akkoyun/WeatherStat_Industrial_Design/P101DA-Rain/M401AA/Readme.md

# H701AA Kepçe Pimi ve Sekmanı  &nbsp; &nbsp; 
| Parça Kodu | Parça Açıklaması | Parça Boyutları | Parça Malzemesi  | Kullanım Adedi |
|---|---|---|---|---|
| H701AA | Kepçe Pimi | ? | Paslanmaz  ? | 1 |
| H602AA | Kepçe Pimi Sekmanı | DIN 6799 Ay Segman 4 mm| Paslanmaz | 2 |

## Açıklama
[Kepçe](../C123AA/Readme.md) , [Alt Gövde](../C122AA/Readme.md)'ye bu Kepçe pimi ile bağlanır.</br>
Pim uçları 4mm DIN 6799 Ay Segman ile sonlandırılır. </br>
# __
### Kepçe Pimi
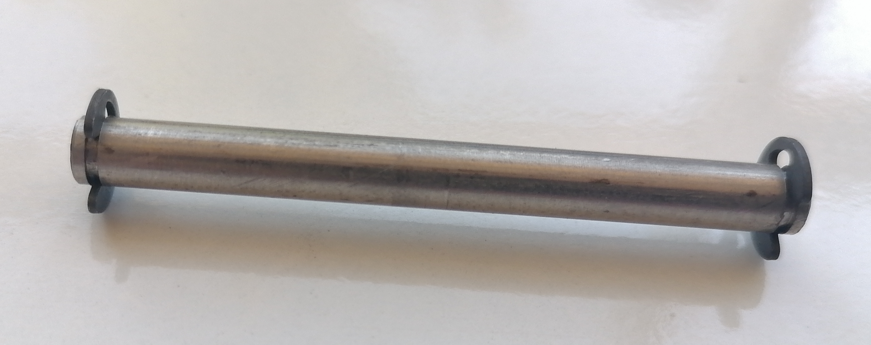
[picture p27: P101DA-Rain/M401AA/2D/kepce_pim.jpg]

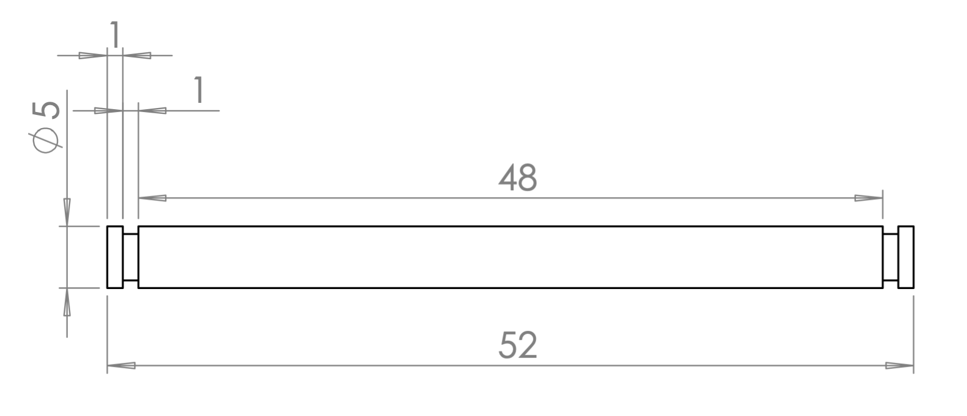
[picture p28: P101DA-Rain/M401AA/2D/kepçe pim teknik resim.png]
