akkoyun/WeatherStat_Industrial_Design/P101DA-Base/C111DA/Documents/README.md

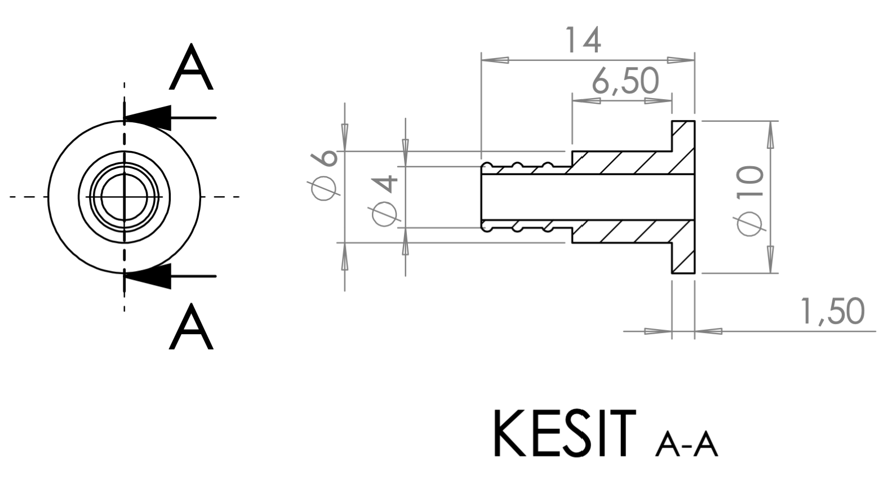
[picture p29: P101DA-Base/C111DA/Documents/ruzgar_pim.png]
Rüzgar Pimi Teknik Resim Rüzgar Pimi


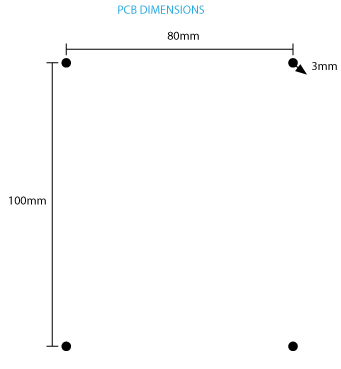
[picture p30: P101DA-Base/C111DA/Documents/PCB-Dimensions.jpg]
PCB Boyutları


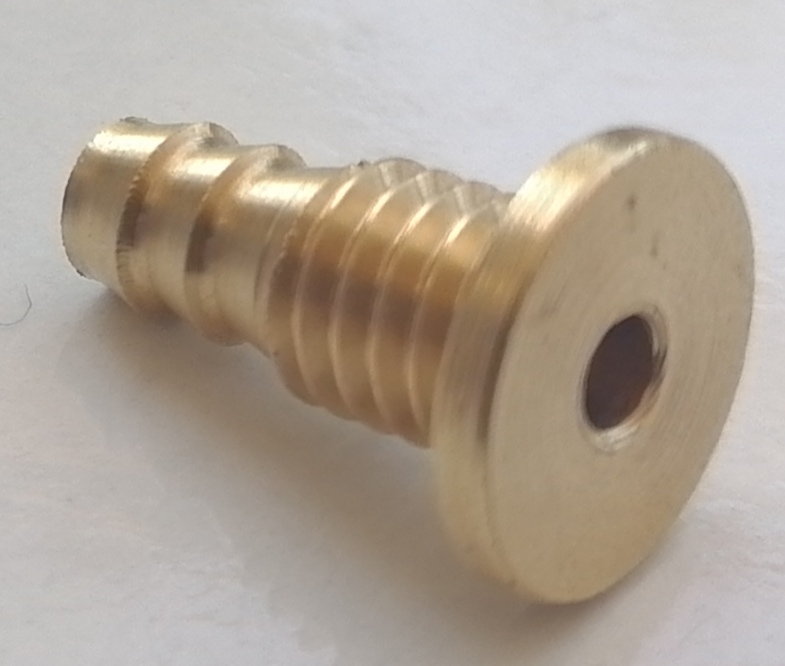
[picture p31: P101DA-Base/C111DA/Documents/ruzgar_pim.jpg]
Rüzgar Pimi


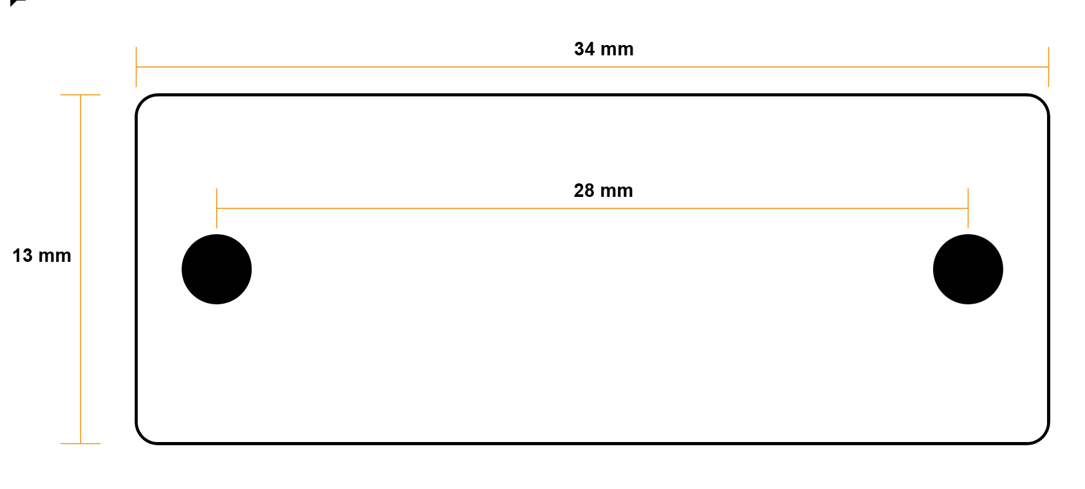
[picture p32: P101DA-Base/C111DA/Documents/UV_PCB_Dimension.png]
UV PCB Dimensions UV PCB Boyutları


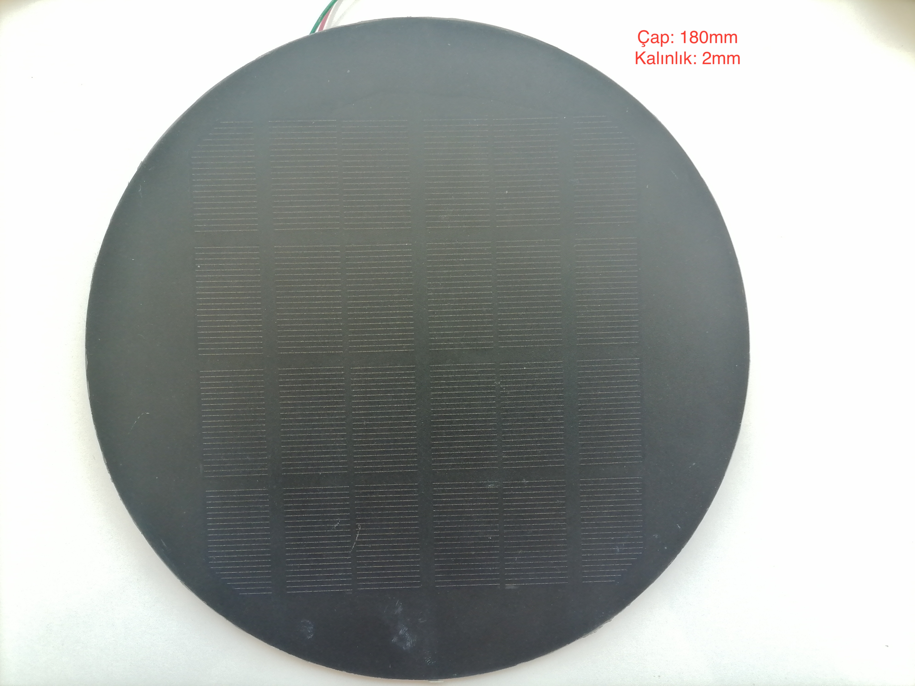
[picture p33: P101DA-Base/C111DA/Documents/solar_panel.jpg]
Solar Panel


700-2700MHZ LTE4G 3G 2G GSM GPRS Omnidirectional High Gain SMA Antenna Whip Antenna 22-24cm
---
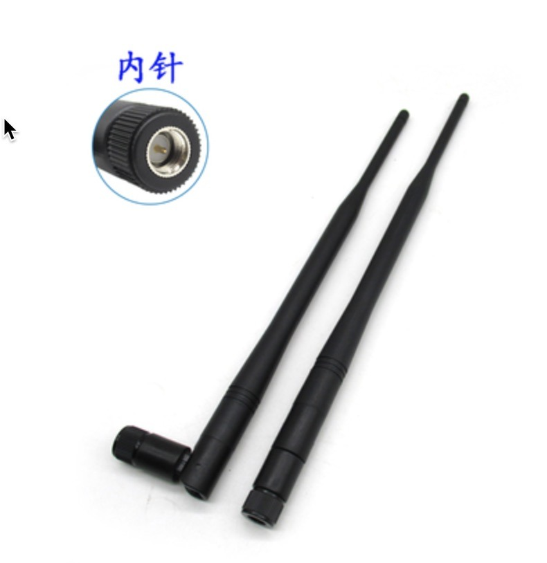
[picture p34: P101DA-Base/C111DA/Documents/GSM_Antenna_Male_SMA.jpeg]
GSM Antenna GSM Anten


[GSM Antenna Link](https://item.taobao.com/item.htm?spm=a230r.1.14.139.7bca162aPO3pgw&id=585446886737&ns=1&abbucket=18#detail)
