akkoyun/WeatherStat_Industrial_Design/P101DA-Rain/C124AA/Readme.md

# C124AA	Taç Kuşkonmaz Pimi  &nbsp; &nbsp; 

| Parça Kodu | Parça Açıklaması | Parça Boyutları | Parça Malzemesi  | Kullanım Adedi |
|---|---|---|---|---|
| C124AA | Taç Kuşkonmaz Pimi | ? | ? | 12 |

## Açıklama
Kuşların cihaz üstüne konmasını engellemek için planlanmıştır. </br>
[Huni](../C121AA/Readme.md) üzerinde deliklere sert şekilde takılır.

## Eksikler ve Yapılacaklar
Hangi malzemeden yapılacağı ve boyutları belirlenecek.</br>
Teknik çizimleri eklenecek</br>
