akkoyun/WeatherStat_Industrial_Design/P101DA-Rain/C125AA/Readme.md

# C125AA	Orta Kuşkonmaz Yuvası  &nbsp; &nbsp; 

| Parça Kodu | Parça Açıklaması | Parça Boyutları | Parça Malzemesi  | Kullanım Adedi |
|---|---|---|---|---|
| C125AA | Orta Kuşkonmaz Yuvası | Q47x42.5 mm | ABS | 1 |

## Açıklama
Kuşların cihaz üstüne konmasını engellemek için planlanmıştır. </br>
[Huni](../C121AA/Readme.md) üzerinde haznenin ortasına sert şekilde takılması planlanmıştır.</br>
Bu parçanın ortasına [C126AA Orta Kuşkonmaz Pimi](../C126AA/Readme.md) sert takılacak şekilde planlanmıştır.

## Eksikler ve Yapılacaklar

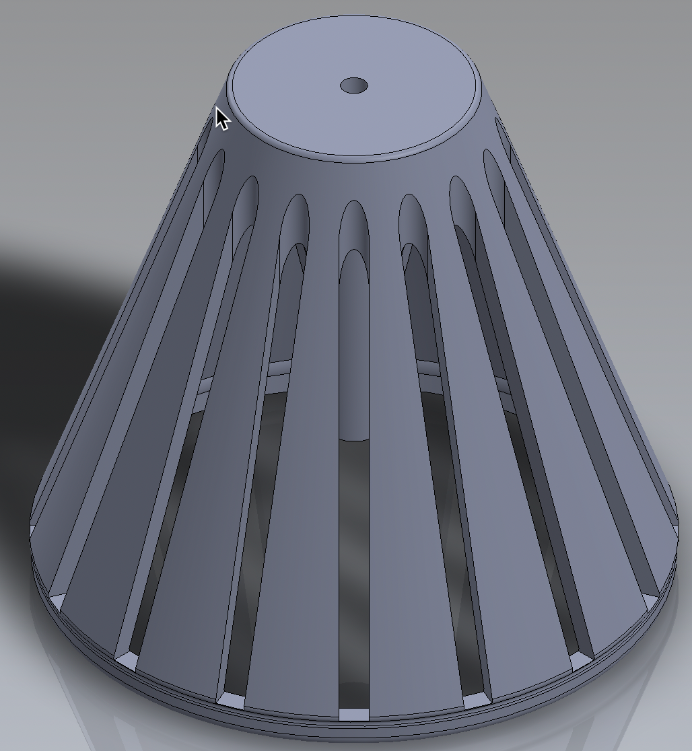
[picture p83: P101DA-Rain/C125AA/2D/1.png]

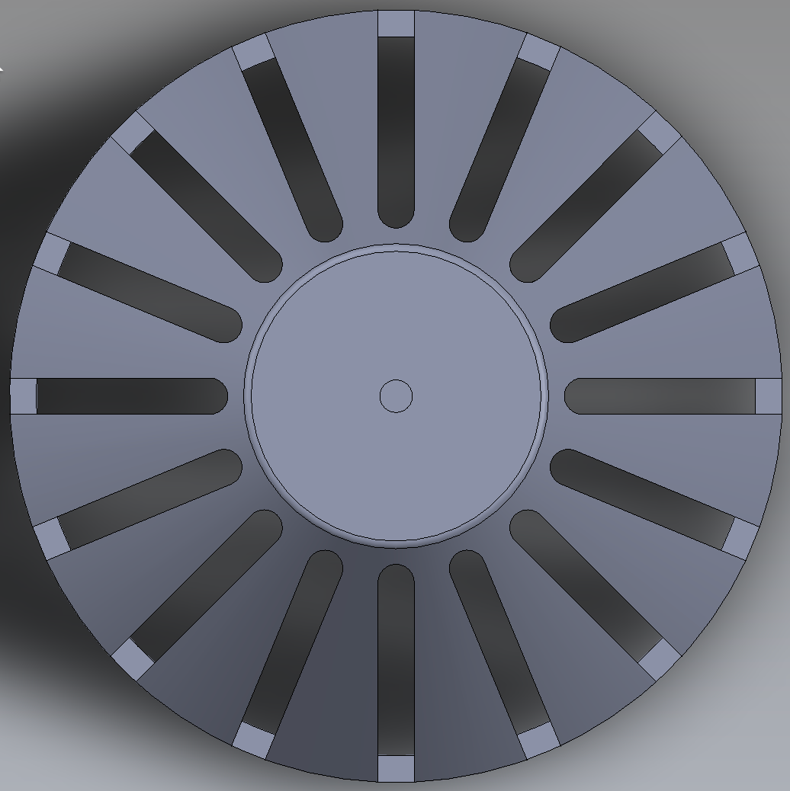
[picture p84: P101DA-Rain/C125AA/2D/2.png]

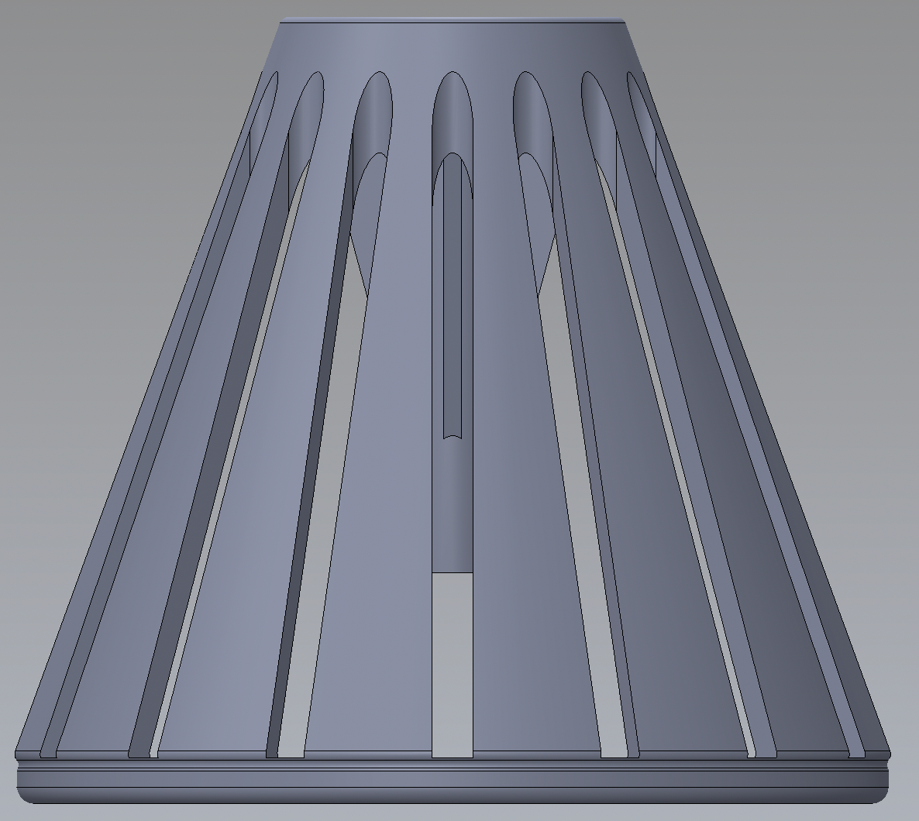
[picture p85: P101DA-Rain/C125AA/2D/3.png]

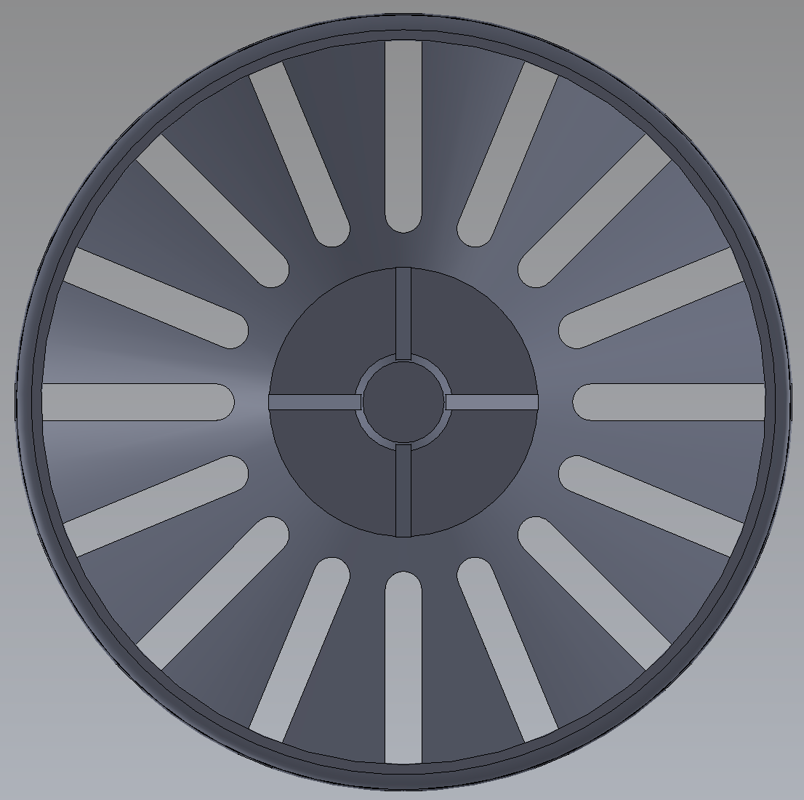
[picture p86: P101DA-Rain/C125AA/2D/4.png]
