akkoyun/WeatherStat_Industrial_Design/P101DA-Rain/C126AA/Readme.md

# C126AA	Orta Kuşkonmaz Pimi  &nbsp; &nbsp; 
| Parça Kodu | Parça Açıklaması | Parça Boyutları | Parça Malzemesi  | Kullanım Adedi |
|---|---|---|---|---|
| C126AA | Orta Kuşkonmaz Pimi | ? | ? | 1 |

## Açıklama
Kuşların cihaz üstüne konmasını engellemek için planlanmıştır. </br>
[C125AA Orta Kuşkonmaz yuvası](../C125AA/Readme.md) üzerine sert şekilde takılır.

## Eksikler ve Yapılacaklar
Hangi malzemeden yapılacağı ve boyutları belirlenecek.</br>
Teknik çizimleri eklenecek</br>
