akkoyun/WeatherStat_Industrial_Design/P101DA-Rain/M101AA/Readme.md

# M101AA YAĞMUR ÜNİTESİ MONTAJ KOLU  &nbsp; &nbsp; 

| Parça Kodu | Parça Açıklaması | Parça Boyutları | Parça Malzemesi  | Kullanım Adedi |
|---|---|---|---|---|
| M101AA | MONTAJ KOLU | ~655x250x3 mm | paslanmaz? | 1 |

## Açıklamalar
Ürün [Direğe]() xxx parçaları ile bağlanır. </br>
Üzerine Yağmur Ünitesininin [Metal Kaidesi M301AA](../M301AA/Readme.md) bağlanır. </br>

## Eksikler ve Yapılacaklar
sldprt dosyası eksik

## 2D

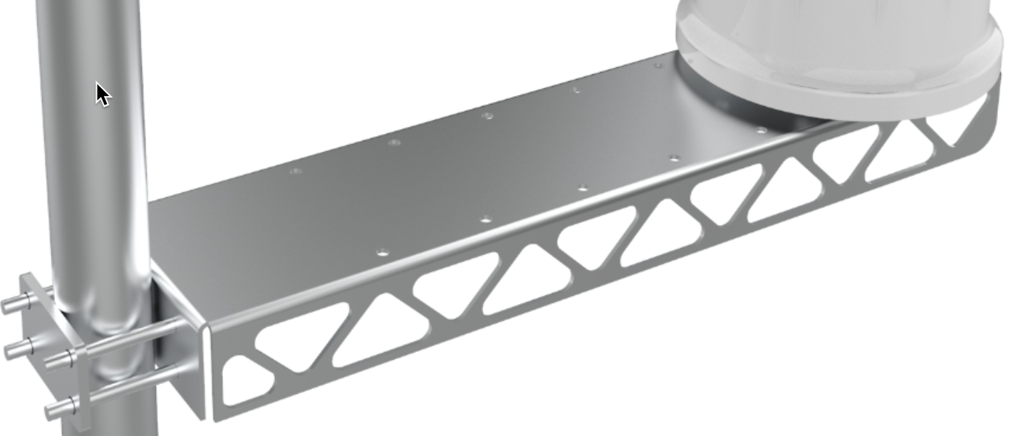
[picture p96: P101DA-Rain/M101AA/2D/1.png]

### DXF Görüntüsü
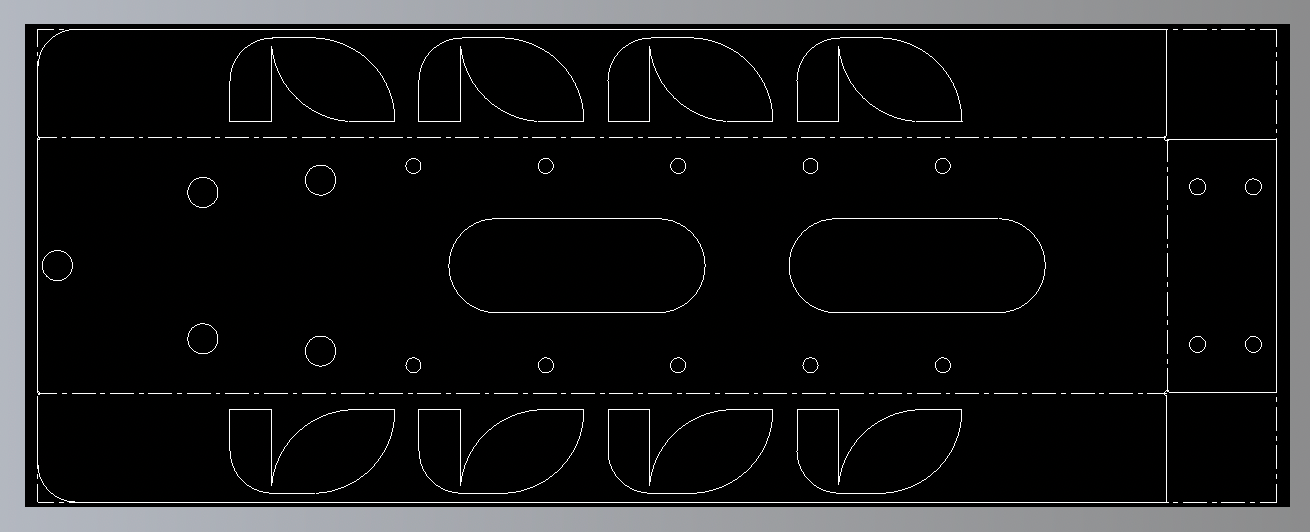
[picture p97: P101DA-Rain/M101AA/2D/2.png]
