akkoyun/WeatherStat_Industrial_Design/P101DA-Rain/M301AA/Readme.md

# M301AA	Metal Kaide  &nbsp; &nbsp; 

| Parça Kodu | Parça Açıklaması | Parça Boyutları | Parça Malzemesi  | Kullanım Adedi |
|---|---|---|---|---|
| M301AA | Metal Kaide | Q214x3 mm | paslanmaz? | 1 |

## Açıklama
Yağmur Ünitesi [Alt Gövde](../C122AA/Readme.md)'sine 4xx vida ile bağlanır.

## Eksikler ve Yapılacaklar
sldprt dosyası yok.</br>
Konnektör bağlantı yeri yok.</br>

## 2D
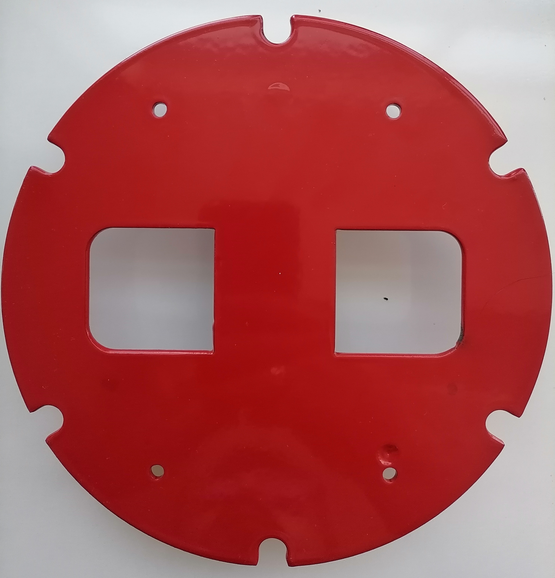
[picture p98: P101DA-Rain/M301AA/2D/1.jpg]


### DXF Görüntüsü
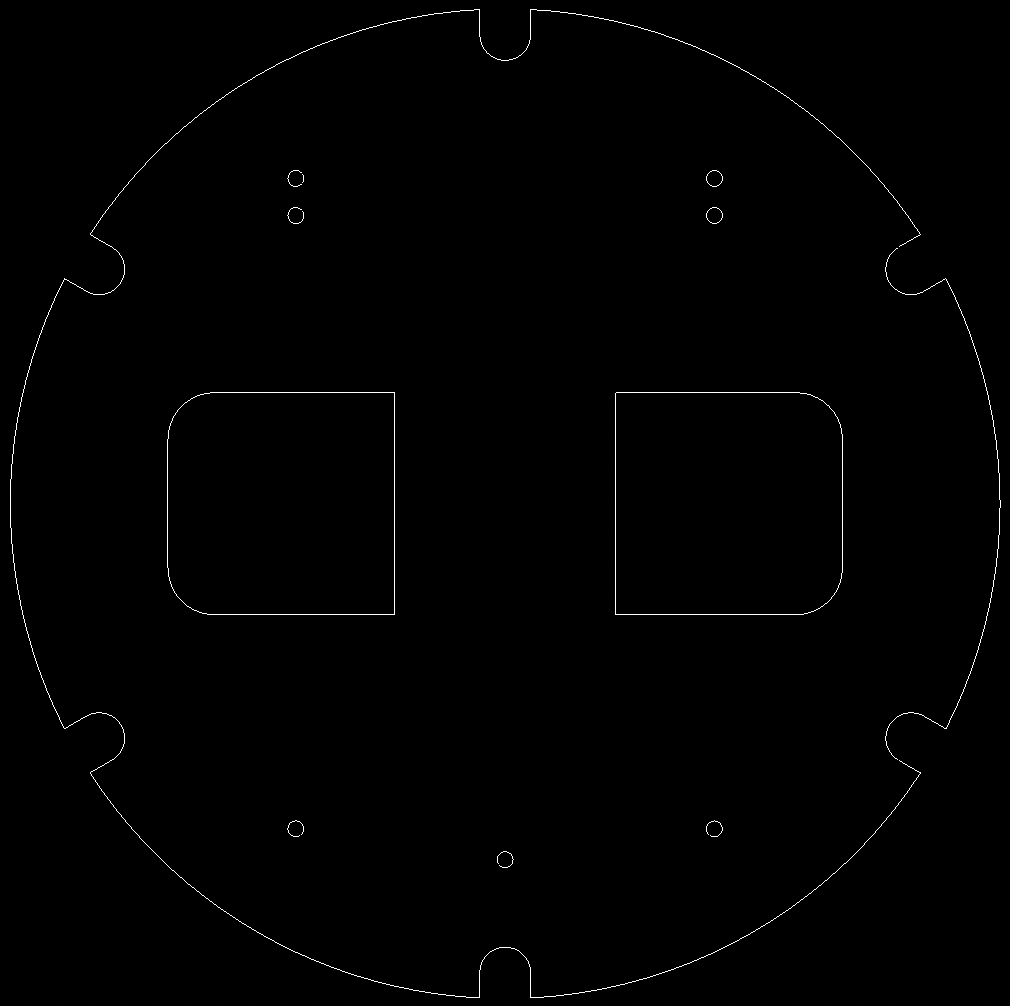
[picture p99: P101DA-Rain/M301AA/2D/2.png]
