akkoyun/WeatherStat_Industrial_Design/P101DA-Rain/M302AA/Readme.md

# M302AA Montaj Kolu-Direk Bağlantı Aparatı  &nbsp; &nbsp; 

| Parça Kodu | Parça Açıklaması | Parça Boyutları | Parça Malzemesi  | Kullanım Adedi |
|---|---|---|---|---|
| C121AA | Montaj Kolu-Direk Bağlantı Aparatı | 108x54x3 mm | paslanmaz? | 1 |

## Açıklama
Montaj Kolunun direğe bağlanması için gereken aparattır. </br>

## Eksikler ve Yapılacaklar
Sldprt dosyası eksik.</br>

## 2D

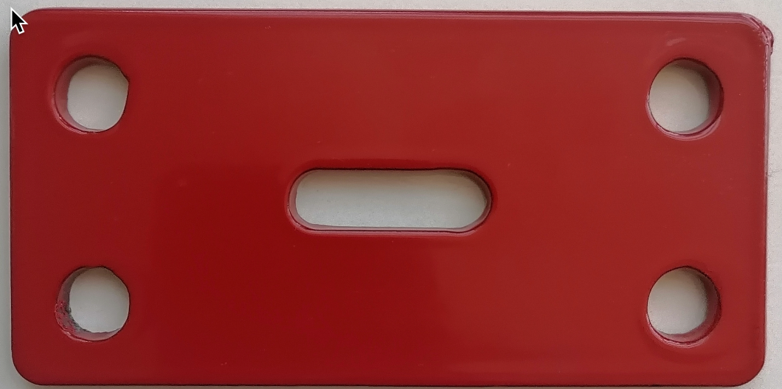
[picture p100: P101DA-Rain/M302AA/2D/1.png]
