akkoyun/WeatherStat_Industrial_Design/P101DA-Base/C111DA/2D/3.png

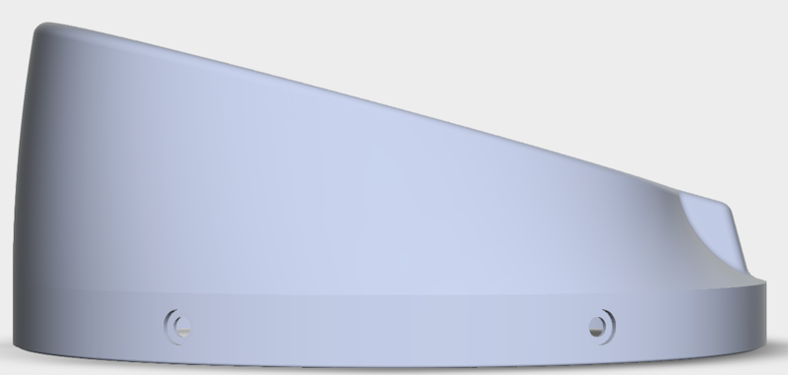
P101DA-Base/C111DA/2D/3.png
