akkoyun/WeatherStat_Industrial_Design/P101DA-Base/C111DA/2D/6.png

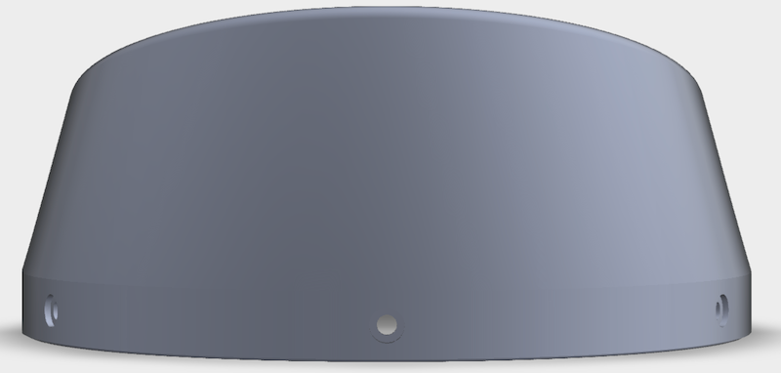
P101DA-Base/C111DA/2D/6.png
