akkoyun/WeatherStat_Industrial_Design/P101DA-Base/C113CA/2D/t/h_sensor_dimensions.png

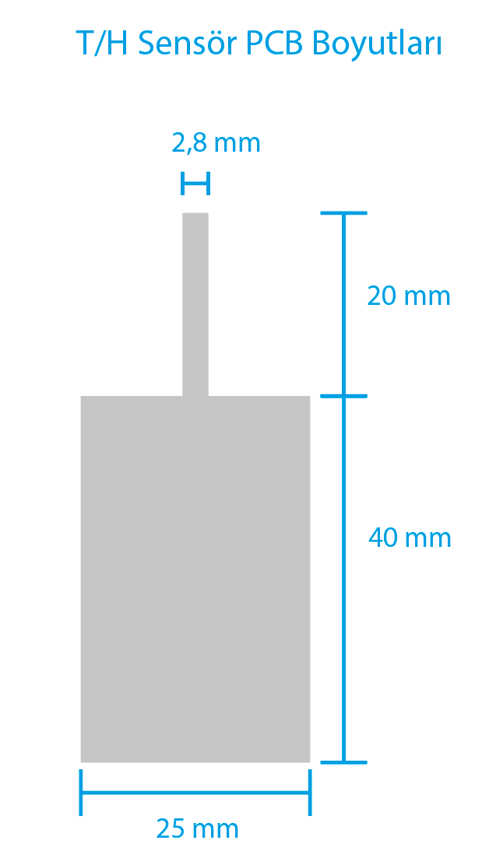
P101DA-Base/C113CA/2D/t/h_sensor_dimensions.png
