akkoyun/WeatherStat_Industrial_Design/P101DA-Rain/C122AA/2D/5.png

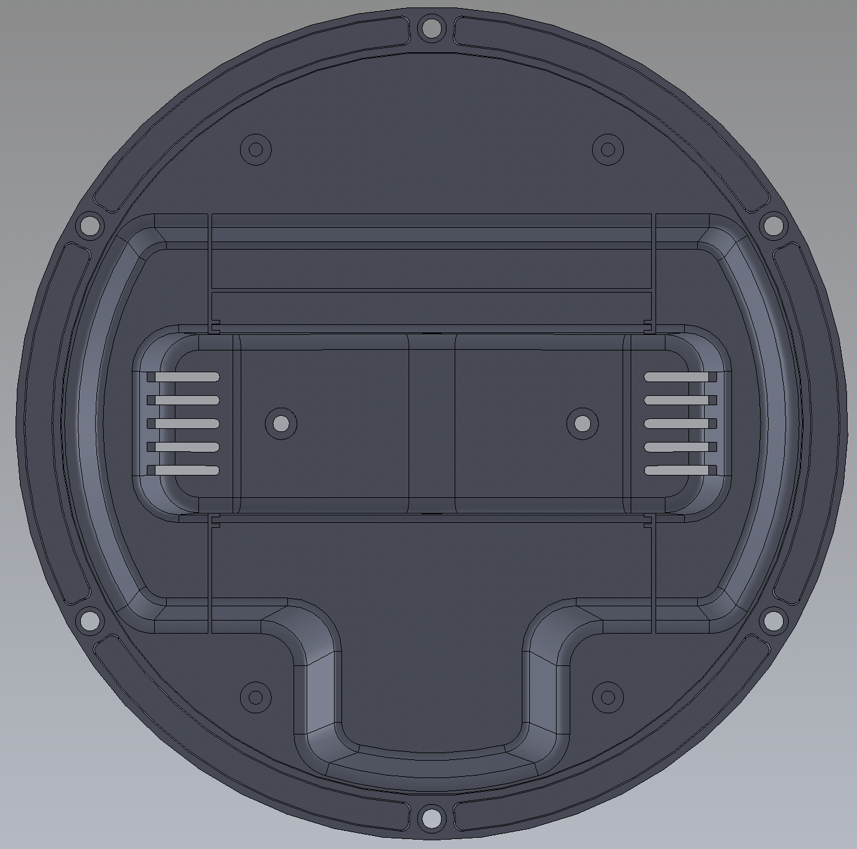
P101DA-Rain/C122AA/2D/5.png
