akkoyun/WeatherStat_Industrial_Design/P101DA-Rain/C122AA/2D/pcb_dimensions.png

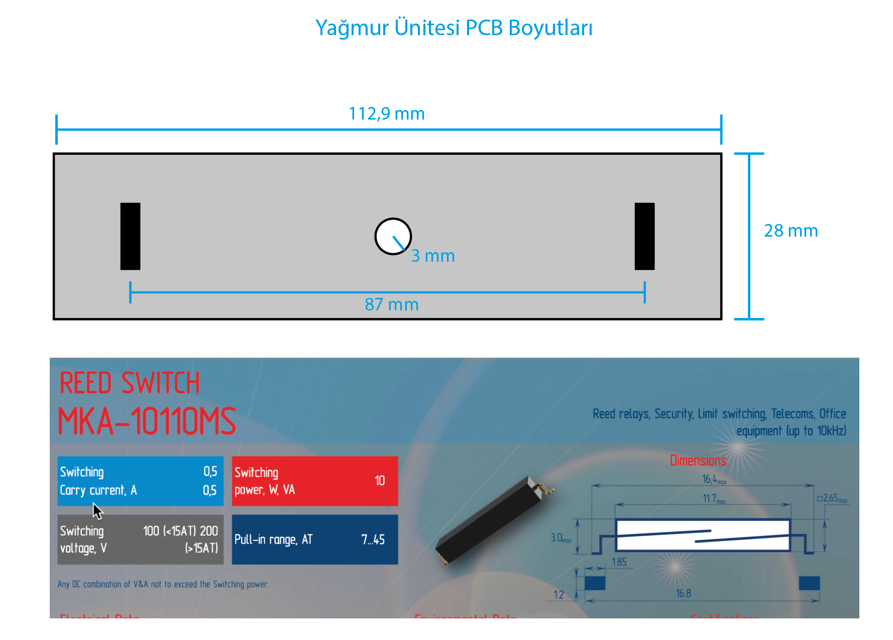
P101DA-Rain/C122AA/2D/pcb_dimensions.png
