akkoyun/WeatherStat_Industrial_Design/P101DA-Rain/Diğer/2D/m4x30yb.png

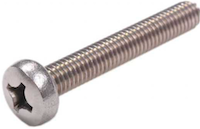
P101DA-Rain/Diğer/2D/m4x30yb.png
