akkoyun/WeatherStat_Industrial_Design/P101DA-Rain/M301AA/2022-09-15_17-42-41.png

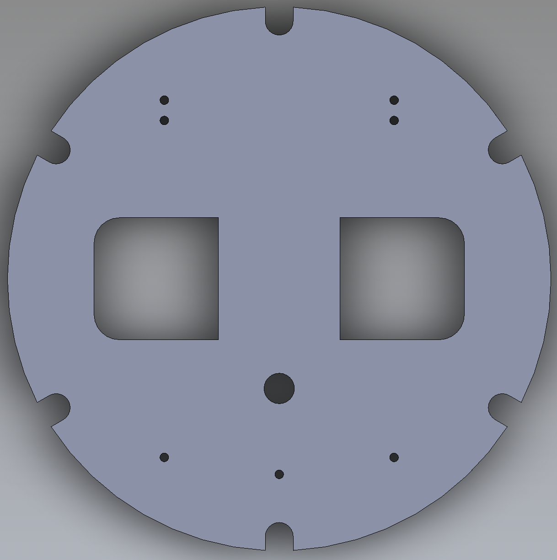
P101DA-Rain/M301AA/2022-09-15_17-42-41.png
