akkoyun/WeatherStat_Industrial_Design/Yönetim Belgeleri/Allfabe Tasarım Sözleşmesi.jpeg

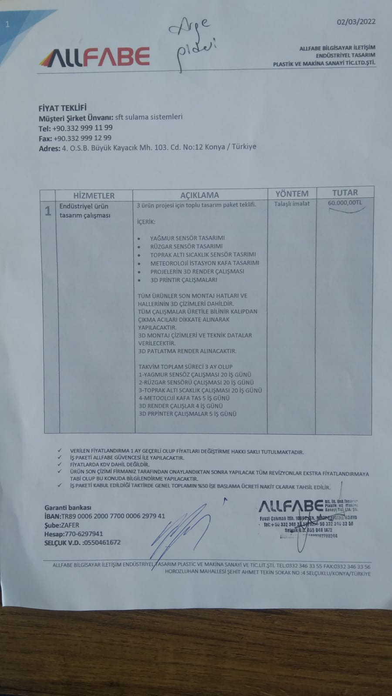
Yönetim Belgeleri/Allfabe Tasarım Sözleşmesi.jpeg
