akkoyun/WeatherStat_Industrial_Design/P101DA-Rain/M301AA/DXF/3mm plastik altı dış 1 adet.DXF

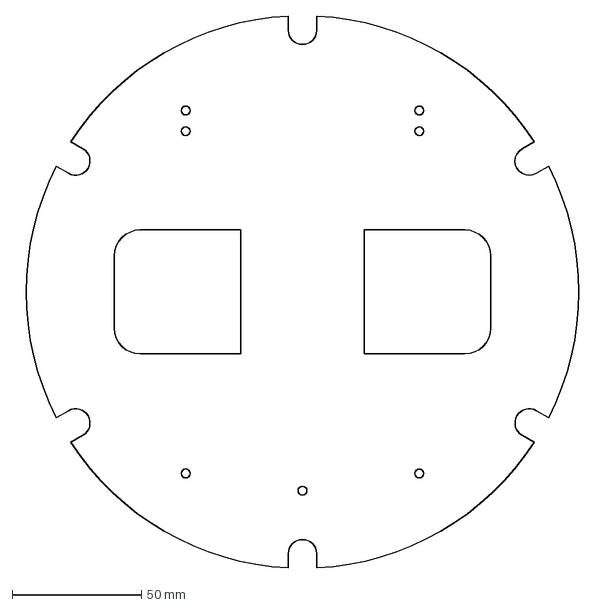
[picture p127: CAD file, 2023-08-27]
P101DA-Rain/M301AA/DXF/3mm plastik altı dış 1 adet.DXF
221.8 x 213.7 mm
