akkoyun/WeatherStat_Industrial_Design/P101DA-Rain/M302AA/3D/M302.STEP

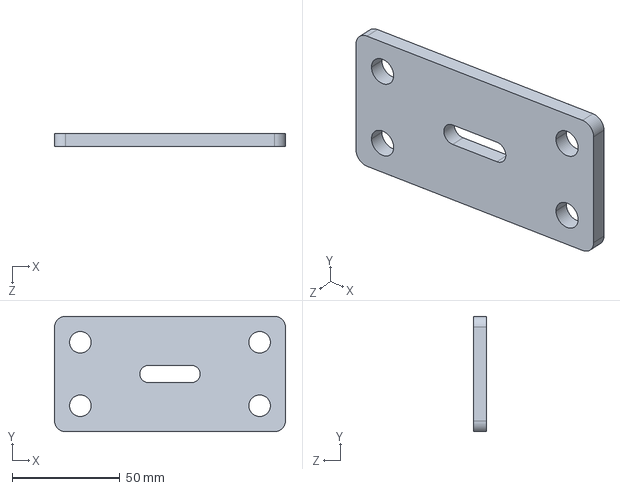
[picture p128: CAD file, 2023-08-27]
P101DA-Rain/M302AA/3D/M302.STEP
107.3 x 53.5 x 6.00 mm
