akkoyun/WeatherStat_Industrial_Design/P101DA-Rain/M302AA/DXF/6MM paslanmaz arka sıktırma 1 adet.DXF

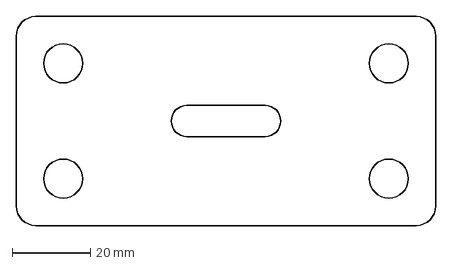
[picture p129: CAD file, 2023-08-27]
P101DA-Rain/M302AA/DXF/6MM paslanmaz arka sıktırma 1 adet.DXF
107.3 x 53.5 mm
