akkoyun/WeatherStat_Industrial_Design/P101DA-Soil/3D/fuar için H904AA yerine.STEP

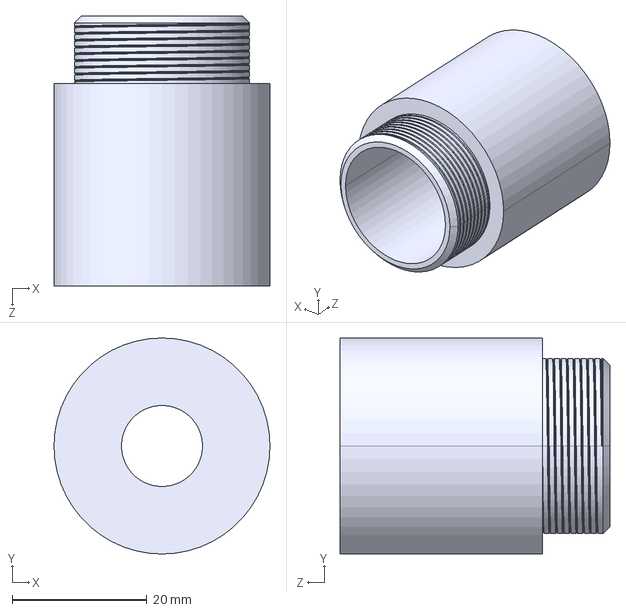
[picture p130: CAD file, 2023-08-27]
P101DA-Soil/3D/fuar için H904AA yerine.STEP
32.0 x 32.0 x 40.0 mm
