akkoyun/WeatherStat_Industrial_Design/P101DA-Soil/3D/H903AA-19 cm.STEP

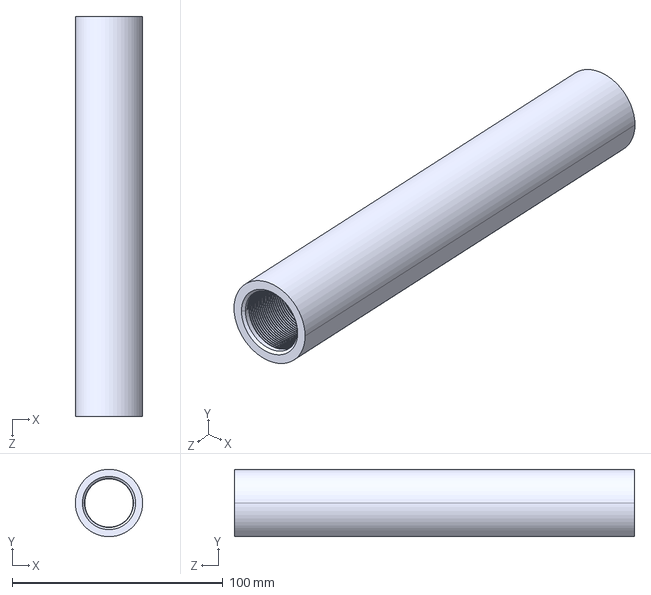
[picture p131: CAD file, 2023-08-27]
P101DA-Soil/3D/H903AA-19 cm.STEP
32.0 x 32.0 x 190.0 mm
