akkoyun/WeatherStat_Industrial_Design/P101DA-Soil/3D/M403AA.STEP

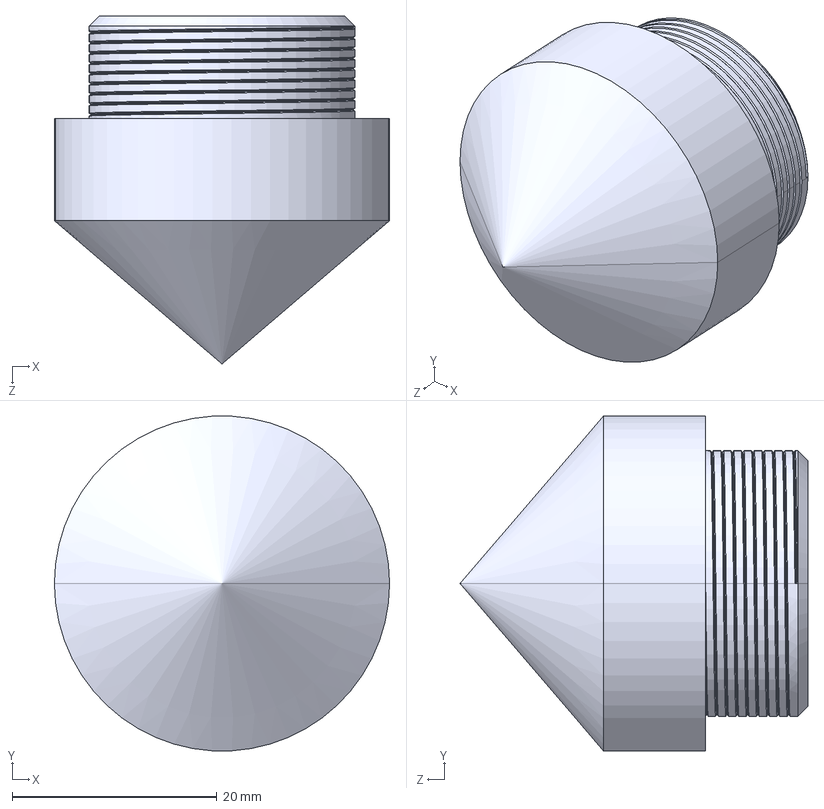
[picture p132: CAD file, 2023-08-27]
P101DA-Soil/3D/M403AA.STEP
32.8 x 32.7 x 34.0 mm
