akkoyun/WeatherStat_Industrial_Design/P101DA-Soil/3D/H903AA-29 cm.STEP

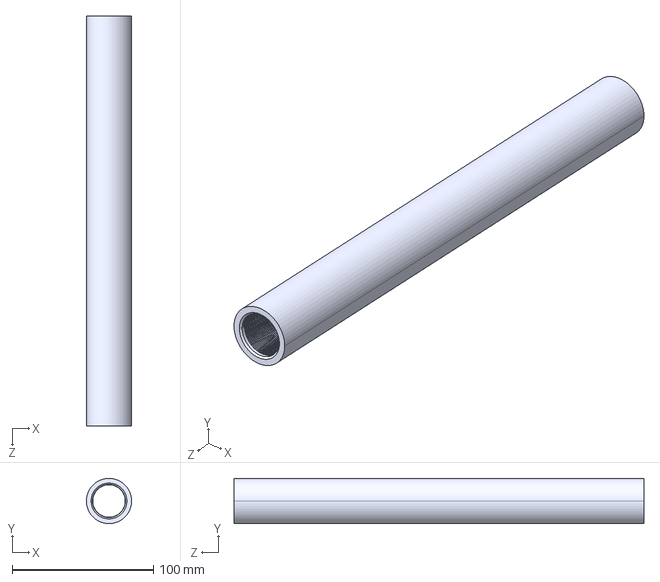
[picture p133: CAD file, 2023-08-27]
P101DA-Soil/3D/H903AA-29 cm.STEP
32.0 x 32.0 x 290.0 mm
