akkoyun/WeatherStat_Industrial_Design/P101DA-Soil/3D/M404AA.STEP

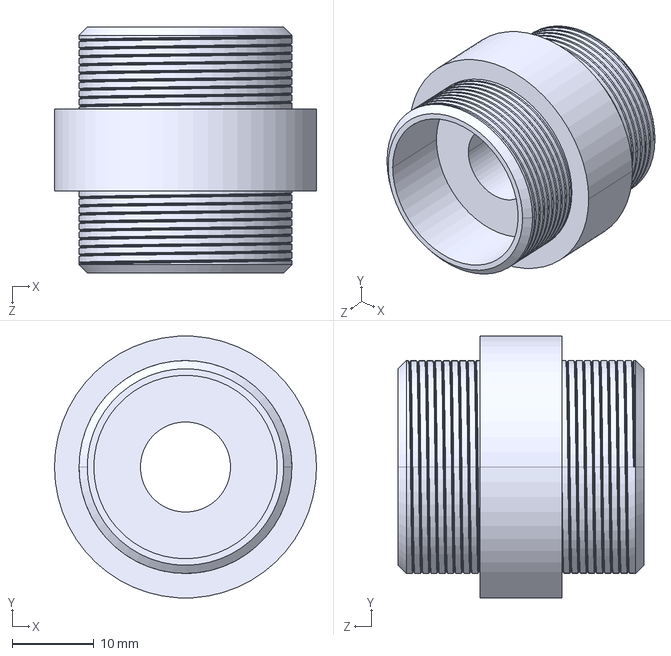
[picture p134: CAD file, 2023-08-27]
P101DA-Soil/3D/M404AA.STEP
32.0 x 31.9 x 30.0 mm
